ChaseStewart/AVR-Annoyatron/Software/AnnoyatronFW/random.h

/*!
 * @file random.h
 *
 * Copyright (c) 2017, ?ukasz Marcin Podkalicki <lpodkalicki@gmail.com>
 *
 * Lightweight library of 16 bit random number generator based on LFSR.
 *
 * Holds definitions and prototypes for the random generator code
 */

#ifndef _RANDOM_H_
#define	_RANDOM_H_


#ifdef	USE_RANDOM_SEED
#define	RANDOM_SEED_ADDRESS	0x00  ///< Setup a pointer to the location of a random seed if USE_RANDOM_SEED is defined
#endif	/* !USE_RANDOM_SEED */

void random_init(uint16_t seed);
uint16_t random(void);
uint16_t adcGetSeed(void);


#endif	/* !_RANDOM_H_ */
